JayGhb/Custom-PCB-Arduino-mini-project/JASON_TSL2561/JASON_TSL2561_U.cpp

/*!
 * @file Adafruit_TSL2561_U.cpp
 *
 * @mainpage Adafruit TSL2561 Light/Lux sensor driver
 *
 * @section intro_sec Introduction
 *
 * This is the documentation for Adafruit's TSL2561 driver for the
 * Arduino platform.  It is designed specifically to work with the
 * Adafruit TSL2561 breakout: http://www.adafruit.com/products/439
 *
 * These sensors use I2C to communicate, 2 pins (SCL+SDA) are required
 * to interface with the breakout.
 *
 * Adafruit invests time and resources providing this open source code,
 * please support Adafruit and open-source hardware by purchasing
 * products from Adafruit!
 *
 * @section dependencies Dependencies
 *
 * This library depends on <a href="https://github.com/adafruit/Adafruit_Sensor">
 * Adafruit_Sensor</a> being present on your system. Please make sure you have
 * installed the latest version before using this library.
 *
 * @section author Author
 *
 * Written by Kevin "KTOWN" Townsend for Adafruit Industries.
 *
 * @section license License
 *
 * BSD license, all text here must be included in any redistribution.
 *
 *   @section  HISTORY
 *
 *   v2.0 - Rewrote driver for Adafruit_Sensor and Auto-Gain support, and
 *          added lux clipping check (returns 0 lux on sensor saturation)
 *   v1.0 - First release (previously TSL2561)
*/
/**************************************************************************/

#include "JASON_TSL2561_U.h"

/*========================================================================*/
/*                            CONSTRUCTORS                                */
/*========================================================================*/

/**************************************************************************/
/*!
    @brief Constructor
    @param addr The I2C address this chip can be found on, 0x29, 0x39 or 0x49
    @param sensorID An optional ID that will be placed in sensor events to help
                    keep track if you have many sensors in use
*/
/**************************************************************************/
JASON_TSLJASON_Unified::JASON_TSLJASON_Unified(uint8_t addr, int32_t sensorID)
{
  _addr = addr;
  _tslJASONInitialised = false;
  _tslJASONAutoGain = false;
  _tslJASONIntegrationTime = TSLJASON_INTEGRATIONTIME_13MS;
  _tslJASONGain = TSLJASON_GAIN_1X;
  _tslJASONSensorID = sensorID;
}

/*========================================================================*/
/*                           PUBLIC FUNCTIONS                             */
/*========================================================================*/

/**************************************************************************/
/*!
    @brief Initializes I2C and configures the sensor with default Wire I2C
           (call this function before doing anything else)
    @returns True if sensor is found and initialized, false otherwise.
*/
/**************************************************************************/
boolean JASON_TSLJASON_Unified::begin()
{
 // _i2c = &SoftwareWire;
  _i2c->begin();
  return init();
}

/**************************************************************************/
/*!
    @brief Initializes I2C and configures the sensor with provided I2C device
           (call this function before doing anything else)
    @param theWire A pointer to any I2C interface (e.g. &Wire1)
    @returns True if sensor is found and initialized, false otherwise.
*/
/**************************************************************************/
boolean JASON_TSLJASON_Unified::begin(SoftwareWire *theWire)
{
  _i2c = theWire;
  _i2c-> begin();
  return init();
}

/**************************************************************************/
/*!
    @brief  Initializes I2C connection and settings. 
    Attempts to determine if the sensor is contactable, then sets up a default
    integration time and gain. Then powers down the chip.
    @returns True if sensor is found and initialized, false otherwise.
*/
/**************************************************************************/
boolean JASON_TSLJASON_Unified::init()
{
  /* Make sure we're actually connected */
  uint8_t x = read8(TSLJASON_REGISTER_ID);
  if (x & 0xF0 != 0x10) { // ID code for TSLJASON
    return false;
  }
  _tslJASONInitialised = true;

  /* Set default integration time and gain */
  setIntegrationTime(_tslJASONIntegrationTime);
  setGain(_tslJASONGain);

  /* Note: by default, the device is in power down mode on bootup */
  disable();

  return true;
}

/**************************************************************************/
/*!
    @brief  Enables or disables the auto-gain settings when reading
            data from the sensor
    @param enable Set to true to enable, False to disable
*/
/**************************************************************************/
void JASON_TSLJASON_Unified::enableAutoRange(bool enable)
{
   _tslJASONAutoGain = enable ? true : false;
}

/**************************************************************************/
/*!
    @brief      Sets the integration time for the TSLJASON. Higher time means
                more light captured (better for low light conditions) but will
		take longer to run readings.
    @param time The amount of time we'd like to add up values
*/
/**************************************************************************/
void JASON_TSLJASON_Unified::setIntegrationTime(tslJASONIntegrationTime_t time)
{
  if (!_tslJASONInitialised) begin();

  /* Enable the device by setting the control bit to 0x03 */
  enable();

  /* Update the timing register */
  write8(TSLJASON_COMMAND_BIT | TSLJASON_REGISTER_TIMING, time | _tslJASONGain);

  /* Update value placeholders */
  _tslJASONIntegrationTime = time;

  /* Turn the device off to save power */
  disable();
}

/**************************************************************************/
/*!
    @brief  Adjusts the gain on the TSLJASON (adjusts the sensitivity to light)
    @param gain The value we'd like to set the gain to
*/
/**************************************************************************/
void JASON_TSLJASON_Unified::setGain(tslJASONGain_t gain)
{
  if (!_tslJASONInitialised) begin();

  /* Enable the device by setting the control bit to 0x03 */
  enable();

  /* Update the timing register */
  write8(TSLJASON_COMMAND_BIT | TSLJASON_REGISTER_TIMING, _tslJASONIntegrationTime | gain);

  /* Update value placeholders */
  _tslJASONGain = gain;

  /* Turn the device off to save power */
  disable();
}

/**************************************************************************/
/*!
    @brief  Gets the broadband (mixed lighting) and IR only values from
            the TSLJASON, adjusting gain if auto-gain is enabled
    @param  broadband Pointer to a uint16_t we will fill with a sensor 
                      reading from the IR+visible light diode.
    @param  ir Pointer to a uint16_t we will fill with a sensor the 
               IR-only light diode.
*/
/**************************************************************************/
void JASON_TSLJASON_Unified::getLuminosity (uint16_t *broadband, uint16_t *ir)
{
  bool valid = false;

  if (!_tslJASONInitialised) begin();

  /* If Auto gain disabled get a single reading and continue */
  if(!_tslJASONAutoGain)
  {
    getData (broadband, ir);
    return;
  }

  /* Read data until we find a valid range */
  bool _agcCheck = false;
  do
  {
    uint16_t _b, _ir;
    uint16_t _hi, _lo;
    tslJASONIntegrationTime_t _it = _tslJASONIntegrationTime;

    /* Get the hi/low threshold for the current integration time */
    switch(_it)
    {
      case TSLJASON_INTEGRATIONTIME_13MS:
        _hi = TSLJASON_AGC_THI_13MS;
        _lo = TSLJASON_AGC_TLO_13MS;
        break;
      case TSLJASON_INTEGRATIONTIME_101MS:
        _hi = TSLJASON_AGC_THI_101MS;
        _lo = TSLJASON_AGC_TLO_101MS;
        break;
      default:
        _hi = TSLJASON_AGC_THI_402MS;
        _lo = TSLJASON_AGC_TLO_402MS;
        break;
    }

    getData(&_b, &_ir);

    /* Run an auto-gain check if we haven't already done so ... */
    if (!_agcCheck)
    {
      if ((_b < _lo) && (_tslJASONGain == TSLJASON_GAIN_1X))
      {
        /* Increase the gain and try again */
        setGain(TSLJASON_GAIN_16X);
        /* Drop the previous conversion results */
        getData(&_b, &_ir);
        /* Set a flag to indicate we've adjusted the gain */
        _agcCheck = true;
      }
      else if ((_b > _hi) && (_tslJASONGain == TSLJASON_GAIN_16X))
      {
        /* Drop gain to 1x and try again */
        setGain(TSLJASON_GAIN_1X);
        /* Drop the previous conversion results */
        getData(&_b, &_ir);
        /* Set a flag to indicate we've adjusted the gain */
        _agcCheck = true;
      }
      else
      {
        /* Nothing to look at here, keep moving ....
           Reading is either valid, or we're already at the chips limits */
        *broadband = _b;
        *ir = _ir;
        valid = true;
      }
    }
    else
    {
      /* If we've already adjusted the gain once, just return the new results.
         This avoids endless loops where a value is at one extreme pre-gain,
         and the the other extreme post-gain */
      *broadband = _b;
      *ir = _ir;
      valid = true;
    }
  } while (!valid);
}



/**************************************************************************/
/*!
    Enables the device
*/
/**************************************************************************/
void JASON_TSLJASON_Unified::enable(void)
{
  /* Enable the device by setting the control bit to 0x03 */
  write8(TSLJASON_COMMAND_BIT | TSLJASON_REGISTER_CONTROL, TSLJASON_CONTROL_POWERON);
}

/**************************************************************************/
/*!
    Disables the device (putting it in lower power sleep mode)
*/
/**************************************************************************/
void JASON_TSLJASON_Unified::disable(void)
{
  /* Turn the device off to save power */
  write8(TSLJASON_COMMAND_BIT | TSLJASON_REGISTER_CONTROL, TSLJASON_CONTROL_POWEROFF);
}

/**************************************************************************/
/*!
    Private function to read luminosity on both channels
*/
/**************************************************************************/
void JASON_TSLJASON_Unified::getData (uint16_t *broadband, uint16_t *ir)
{
  /* Enable the device by setting the control bit to 0x03 */
  enable();

  /* Wait x ms for ADC to complete */
  switch (_tslJASONIntegrationTime)
  {
    case TSLJASON_INTEGRATIONTIME_13MS:
      delay(TSLJASON_DELAY_INTTIME_13MS);  // KTOWN: Was 14ms
      break;
    case TSLJASON_INTEGRATIONTIME_101MS:
      delay(TSLJASON_DELAY_INTTIME_101MS); // KTOWN: Was 102ms
      break;
    default:
      delay(TSLJASON_DELAY_INTTIME_402MS); // KTOWN: Was 403ms
      break;
  }

  /* Reads a two byte value from channel 0 (visible + infrared) */
  *broadband = read16(TSLJASON_COMMAND_BIT | TSLJASON_WORD_BIT | TSLJASON_REGISTER_CHAN0_LOW);

  /* Reads a two byte value from channel 1 (infrared) */
  *ir = read16(TSLJASON_COMMAND_BIT | TSLJASON_WORD_BIT | TSLJASON_REGISTER_CHAN1_LOW);

  /* Turn the device off to save power */
  disable();
}


/**************************************************************************/
/*!
    @brief  Converts the raw sensor values to the standard SI lux equivalent.
    @param  broadband The 16-bit sensor reading from the IR+visible light diode.
    @param  ir The 16-bit sensor reading from the IR-only light diode.
    @returns The integer Lux value we calcuated. 
             Returns 0 if the sensor is saturated and the values are 
             unreliable, or 65536 if the sensor is saturated.
*/
/**************************************************************************/
/**************************************************************************/
/*!
    
    Returns 
*/
/**************************************************************************/
uint32_t JASON_TSLJASON_Unified::calculateLux(uint16_t broadband, uint16_t ir)
{
  unsigned long chScale;
  unsigned long channel1;
  unsigned long channel0;

  /* Make sure the sensor isn't saturated! */
  uint16_t clipThreshold;
  switch (_tslJASONIntegrationTime)
  {
    case TSLJASON_INTEGRATIONTIME_13MS:
      clipThreshold = TSLJASON_CLIPPING_13MS;
      break;
    case TSLJASON_INTEGRATIONTIME_101MS:
      clipThreshold = TSLJASON_CLIPPING_101MS;
      break;
    default:
      clipThreshold = TSLJASON_CLIPPING_402MS;
      break;
  }

  /* Return 65536 lux if the sensor is saturated */
  if ((broadband > clipThreshold) || (ir > clipThreshold))
  {
    return 65536;
  }

  /* Get the correct scale depending on the intergration time */
  switch (_tslJASONIntegrationTime)
  {
    case TSLJASON_INTEGRATIONTIME_13MS:
      chScale = TSLJASON_LUX_CHSCALE_TINT0;
      break;
    case TSLJASON_INTEGRATIONTIME_101MS:
      chScale = TSLJASON_LUX_CHSCALE_TINT1;
      break;
    default: /* No scaling ... integration time = 402ms */
      chScale = (1 << TSLJASON_LUX_CHSCALE);
      break;
  }

  /* Scale for gain (1x or 16x) */
  if (!_tslJASONGain) chScale = chScale << 4;

  /* Scale the channel values */
  channel0 = (broadband * chScale) >> TSLJASON_LUX_CHSCALE;
  channel1 = (ir * chScale) >> TSLJASON_LUX_CHSCALE;

  /* Find the ratio of the channel values (Channel1/Channel0) */
  unsigned long ratio1 = 0;
  if (channel0 != 0) ratio1 = (channel1 << (TSLJASON_LUX_RATIOSCALE+1)) / channel0;

  /* round the ratio value */
  unsigned long ratio = (ratio1 + 1) >> 1;

  unsigned int b, m;

#ifdef TSLJASON_PACKAGE_CS
  if ((ratio >= 0) && (ratio <= TSLJASON_LUX_K1C))
    {b=TSLJASON_LUX_B1C; m=TSLJASON_LUX_M1C;}
  else if (ratio <= TSLJASON_LUX_K2C)
    {b=TSLJASON_LUX_B2C; m=TSLJASON_LUX_M2C;}
  else if (ratio <= TSLJASON_LUX_K3C)
    {b=TSLJASON_LUX_B3C; m=TSLJASON_LUX_M3C;}
  else if (ratio <= TSLJASON_LUX_K4C)
    {b=TSLJASON_LUX_B4C; m=TSLJASON_LUX_M4C;}
  else if (ratio <= TSLJASON_LUX_K5C)
    {b=TSLJASON_LUX_B5C; m=TSLJASON_LUX_M5C;}
  else if (ratio <= TSLJASON_LUX_K6C)
    {b=TSLJASON_LUX_B6C; m=TSLJASON_LUX_M6C;}
  else if (ratio <= TSLJASON_LUX_K7C)
    {b=TSLJASON_LUX_B7C; m=TSLJASON_LUX_M7C;}
  else if (ratio > TSLJASON_LUX_K8C)
    {b=TSLJASON_LUX_B8C; m=TSLJASON_LUX_M8C;}
#else
  if ((ratio >= 0) && (ratio <= TSLJASON_LUX_K1T))
    {b=TSLJASON_LUX_B1T; m=TSLJASON_LUX_M1T;}
  else if (ratio <= TSLJASON_LUX_K2T)
    {b=TSLJASON_LUX_B2T; m=TSLJASON_LUX_M2T;}
  else if (ratio <= TSLJASON_LUX_K3T)
    {b=TSLJASON_LUX_B3T; m=TSLJASON_LUX_M3T;}
  else if (ratio <= TSLJASON_LUX_K4T)
    {b=TSLJASON_LUX_B4T; m=TSLJASON_LUX_M4T;}
  else if (ratio <= TSLJASON_LUX_K5T)
    {b=TSLJASON_LUX_B5T; m=TSLJASON_LUX_M5T;}
  else if (ratio <= TSLJASON_LUX_K6T)
    {b=TSLJASON_LUX_B6T; m=TSLJASON_LUX_M6T;}
  else if (ratio <= TSLJASON_LUX_K7T)
    {b=TSLJASON_LUX_B7T; m=TSLJASON_LUX_M7T;}
  else if (ratio > TSLJASON_LUX_K8T)
    {b=TSLJASON_LUX_B8T; m=TSLJASON_LUX_M8T;}
#endif

  unsigned long temp;
  temp = ((channel0 * b) - (channel1 * m));

  /* Do not allow negative lux value */
  if (temp < 0) temp = 0;

  /* Round lsb (2^(LUX_SCALE-1)) */
  temp += (1 << (TSLJASON_LUX_LUXSCALE-1));

  /* Strip off fractional portion */
  uint32_t lux = temp >> TSLJASON_LUX_LUXSCALE;

  /* Signal I2C had no errors */
  return lux;
}

/**************************************************************************/
/*!
    @brief  Gets the most recent sensor event
    @param  event Pointer to a sensor_event_t type that will be filled 
                  with the lux value, timestamp, data type and sensor ID.
    @returns True if sensor reading is between 0 and 65535 lux, 
             false if sensor is saturated
*/
/**************************************************************************/
bool JASON_TSLJASON_Unified::getEvent(sensors_event_t *event)
{
  uint16_t broadband, ir;

  /* Clear the event */
  memset(event, 0, sizeof(sensors_event_t));

  event->version   = sizeof(sensors_event_t);
  event->sensor_id = _tslJASONSensorID;
  event->type      = SENSOR_TYPE_LIGHT;
  event->timestamp = millis();

  /* Calculate the actual lux value */
  getLuminosity(&broadband, &ir);
  event->light = calculateLux(broadband, ir);

  if (event->light == 65536) {
    return false;
  }
  return true;
}

/**************************************************************************/
/*!
    @brief  Gets the sensor_t data
    @param  sensor A pointer to a sensor_t structure that we will fill with
                   details about the TSLJASON and its capabilities
*/
/**************************************************************************/
void JASON_TSLJASON_Unified::getSensor(sensor_t *sensor)
{
  /* Clear the sensor_t object */
  memset(sensor, 0, sizeof(sensor_t));

  /* Insert the sensor name in the fixed length char array */
  strncpy (sensor->name, "TSLJASON", sizeof(sensor->name) - 1);
  sensor->name[sizeof(sensor->name)- 1] = 0;
  sensor->version     = 1;
  sensor->sensor_id   = _tslJASONSensorID;
  sensor->type        = SENSOR_TYPE_LIGHT;
  sensor->min_delay   = 0;
  sensor->max_value   = 17000.0;  /* Based on trial and error ... confirm! */
  sensor->min_value   = 1.0;
  sensor->resolution  = 1.0;
}



/*========================================================================*/
/*                          PRIVATE FUNCTIONS                             */
/*========================================================================*/

/**************************************************************************/
/*!
    @brief  Writes a register and an 8 bit value over I2C
    @param  reg I2C register to write the value to
    @param  value The 8-bit value we're writing to the register
*/
/**************************************************************************/
void JASON_TSLJASON_Unified::write8 (uint8_t reg, uint8_t value)
{
  _i2c->beginTransmission(_addr);
  _i2c->write(reg);
  _i2c->write(value);
  _i2c->endTransmission();
}

/**************************************************************************/
/*!
    @brief  Reads an 8 bit value over I2C
    @param  reg I2C register to read from
    @returns 8-bit value containing single byte data read
*/
/**************************************************************************/
uint8_t JASON_TSLJASON_Unified::read8(uint8_t reg)
{
  _i2c->beginTransmission(_addr);
  _i2c->write(reg);
  _i2c->endTransmission();

  _i2c->requestFrom(_addr, 1);
  return _i2c-> read();
}

/**************************************************************************/
/*!
    @brief  Reads a 16 bit values over I2C
    @param  reg I2C register to read from
    @returns 16-bit value containing 2-byte data read
*/
/**************************************************************************/
uint16_t JASON_TSLJASON_Unified::read16(uint8_t reg)
{
  uint16_t x, t;

  _i2c->beginTransmission(_addr);
  _i2c->write(reg);
  _i2c->endTransmission();

  _i2c->requestFrom(_addr, 2);
  t = _i2c->read();
  x = _i2c->read();
  x <<= 8;
  x |= t;
  return x;
}
